txrxau/one-rom/hardware/pcb/verified/fire-24-f/README.md

# Fire 24 Rev F

A second USB-C variant, retaining the RP2354A MCU.

Changes from fire-24-e:
- Adds a neo-pixel LED, sharing GPIO 29 with the status LED.
- SEL pins have been swapped around for consistency with the latest 28, 32 and 40 pin designs.  The two right-most SEL pins are now ADC (non-5V tolerant) pins, with the othe two being 5V tolerant.
- A fraction of a mm narrower and shorter.
