txrxau/one-rom/rust/fw-emulator/build.rs

// Copyright (C) 2026 Piers Finlayson <piers@piers.rocks>
//
// MIT License

use std::{
    env,
    panic::{AssertUnwindSafe, catch_unwind},
    path::PathBuf,
    process::Command,
};

// Not defaults — used in error messages to show the caller what to set.
const EXAMPLE_CONFIG: &str = "onerom-config/test-0.json";
const EXAMPLE_BOARD: &str = "fire-24-a";

fn main() {
    let manifest_dir = PathBuf::from(env::var("CARGO_MANIFEST_DIR").unwrap());

    // Structure: project/rust/onerom-fw-emulator  →  two parents  →  project/
    let project_root = manifest_dir
        .parent()
        .expect("missing rust/ parent")
        .parent()
        .expect("missing project root")
        .to_path_buf();

    let c_root = project_root.join("firmware");

    let config = env::var("CONFIG")
        .unwrap_or_else(|_| panic!("CONFIG must be set (e.g. CONFIG={EXAMPLE_CONFIG})"));
    let board = env::var("BOARD")
        .unwrap_or_else(|_| panic!("BOARD must be set (e.g. BOARD={EXAMPLE_BOARD})"));

    // BASE_DIR is the project root used to resolve relative CONFIG paths and
    // ROM image files.  Defaults to the computed project_root so the Makefile
    // shell-script build works without change; set it explicitly when invoking
    // cargo from a different directory (e.g. BASE_DIR=$(realpath ../..) from
    // fw-tester/).
    let base_dir = if let Ok(bd) = env::var("BASE_DIR") {
        std::fs::canonicalize(&bd)
            .unwrap_or_else(|e| panic!("Cannot resolve BASE_DIR '{}': {}", bd, e))
    } else {
        project_root.clone()
    };

    // Resolve CONFIG to a canonical absolute path relative to base_dir.
    // Absolute paths are used as-is.
    let config_abs = {
        let p = PathBuf::from(&config);
        if p.is_absolute() {
            std::fs::canonicalize(&p)
                .unwrap_or_else(|e| panic!("Cannot find CONFIG '{}': {}", config, e))
        } else {
            std::fs::canonicalize(base_dir.join(&p)).unwrap_or_else(|e| {
                panic!(
                    "Cannot find CONFIG '{}' relative to BASE_DIR '{}': {}",
                    config,
                    base_dir.display(),
                    e
                )
            })
        }
    };

    // Re-run build.rs if these env vars change.
    println!("cargo:rerun-if-env-changed=CONFIG");
    println!("cargo:rerun-if-env-changed=BOARD");
    println!("cargo:rerun-if-env-changed=BASE_DIR");

    // ── C build ──────────────────────────────────────────────────────────────

    // Cargo sets CARGO_CFG_TARGET_ARCH to the *target* being built.  When that
    // is wasm we cross-compile the C library with Emscripten (for One ROM Lens)
    // into a separate build-wasm/, instead of the native host build-test/.  The
    // native path is unchanged.
    let is_wasm = env::var("CARGO_CFG_TARGET_ARCH").as_deref() == Ok("wasm32");
    let (make_target, clean_target, build_subdir) = if is_wasm {
        (
            "libonerom-test-wasm",
            "clean-libonerom-test-wasm",
            "build-wasm",
        )
    } else {
        ("libonerom-test", "clean-libonerom-test", "build-test")
    };

    println!(
        "cargo:rerun-if-changed={}",
        project_root.join("Makefile").display()
    );
    println!("cargo:rerun-if-changed={}", c_root.display());
    println!("cargo:rerun-if-changed={}", config_abs.display());
    println!(
        "cargo:rerun-if-changed={}",
        manifest_dir.join("src/wrapper.h").display()
    );

    // Clean the C library if CONFIG or BOARD has changed since the last build.
    // The Makefile has no visibility into these variables, so we track them
    // ourselves via a stamp file in the build output directory.
    let stamp_path = c_root.join(build_subdir).join(".build-config");
    let stamp = format!("CONFIG={}\nBOARD={board}\n", config_abs.display());
    let needs_clean = std::fs::read_to_string(&stamp_path)
        .map(|s| s != stamp)
        .unwrap_or(true);

    if needs_clean {
        let _ = Command::new("make")
            .arg("-C")
            .arg(&project_root)
            .arg(clean_target)
            .env("CONFIG", &config_abs)
            .env("BOARD", &board)
            .status()
            .expect("could not run make clean target");
    }

    let status = Command::new("make")
        .arg("-C")
        .arg(&project_root)
        .arg(make_target)
        .env("CONFIG", &config_abs)
        .env("BOARD", &board)
        .status()
        .expect("could not run make — is it on PATH?");
    assert!(
        status.success(),
        "make {make_target} failed (CONFIG={} BOARD={board})",
        config_abs.display()
    );

    std::fs::write(&stamp_path, &stamp).expect("could not write build stamp");

    // ── Linking ──────────────────────────────────────────────────────────────

    println!(
        "cargo:rustc-link-search=native={}",
        c_root.join(build_subdir).display()
    );
    println!("cargo:rustc-link-lib=static=onerom-test");
    // Emscripten provides libm as part of its libc; only the native build needs
    // an explicit -lm.
    if !is_wasm {
        println!("cargo:rustc-link-lib=m");
    }

    // ── bindgen ──────────────────────────────────────────────────────────────

    // Parse the firmware headers for the host explicitly, rather than leaving
    // libclang to use its own default target.  Two cases need this:
    //
    //   - Cross-compiling to wasm: cargo sets TARGET=wasm32-unknown-emscripten,
    //     so libclang would parse for the wasm target and fail to find the libc
    //     headers (string.h etc.), which live in the Emscripten sysroot.
    //   - A native build where LIBCLANG_PATH names a cross-toolchain's libclang
    //     (an ESP or AVR toolchain on PATH, say).  Its default target has no
    //     host sysroot, so the same headers go missing, and the pointer width
    //     it reports does not match the Rust target.
    //
    // We only need the C *declarations* — no by-value C structs cross the FFI
    // boundary whose layout differs between host and target — so parsing with
    // the host target and its system headers is safe.  bindgen emits
    // width-correct type aliases (c_long, usize, …) regardless of the parse
    // target.
    let builder = bindgen::Builder::default()
        .header(manifest_dir.join("src/wrapper.h").to_str().unwrap())
        .clang_arg(format!("--target={}", env::var("HOST").unwrap()));

    let builder = builder
        .clang_arg(format!("-I{}", c_root.join("include").display()))
        .clang_arg(format!("-I{}", c_root.join("generated").display()))
        .clang_arg(format!("-I{}", c_root.join("include/test").display()))
        .clang_arg(format!("-I{}", c_root.join("apio/include").display()))
        .clang_arg(format!("-I{}", c_root.join("epio/include").display()))
        .clang_arg(format!("-I{}", c_root.join("ora").display()))
        .clang_arg("-DTEST_BUILD=1".to_string())
        .clang_arg("-DDEBUG_LOGGING=1".to_string())
        .allowlist_function("firmware_main")
        .allowlist_function("epio_from_apio")
        .allowlist_function("epio_get_sram_ptr")
        .allowlist_function("epio_update_from_apio")
        .allowlist_function("epio_drive_gpios_ext")
        .allowlist_function("epio_read_pin_states")
        .allowlist_function("epio_step_cycles")
        .allowlist_function("epio_free")
        .allowlist_function("epio_read_driven_pins")
        .allowlist_function("epio_read_pull_up_pins")
        .allowlist_function("epio_read_pull_down_pins")
        .allowlist_function("epio_disassemble_sm")
        .allowlist_function("epio_get_gpio_input_inverted")
        .allowlist_function("set_host_sram_ptr")
        .allowlist_function("stub_set_sel_image")
        .allowlist_function("stub_set_rp_variant")
        .allowlist_function("ffi_limp_mode")
        .allowlist_function("ffi_pios_enabled")
        .allowlist_function("ffi_image_sel")
        .allowlist_function("ffi_epio_setup_sram")
        .allowlist_function("ffi_epio_setup_dma_chain")
        .allowlist_function("ffi_epio_arm_monitor")
        .allowlist_function("set_onerom_test_yield_hook")
        .allowlist_function("ffi_set_logging")
        .allowlist_function("ffi_serving_alg")
        .allowlist_type("ffi_serving_alg_t")
        // The algorithm enums the reported ids belong to: a test that maps an
        // id to an expected cycle cost must name the enumerators rather than
        // hardcode their values.
        .allowlist_type("onerom_alg_cs_t")
        .allowlist_type("onerom_alg_addr_t")
        .allowlist_type("onerom_alg_data_t")
        .allowlist_function("ora_fn_lookup")
        .allowlist_type("ora_result_t")
        .allowlist_type("ora_.*_fn_t")
        // ora_gpio_use_t / ora_gpio_state_t are referenced only from comments
        // and uint8_t struct fields, so nothing drags them in transitively.
        // The plugin API tester compares ora_gpio_query's reported use against
        // the apio emulation's own record, and must name the enumerators
        // rather than hardcode their values.
        .allowlist_type("ora_gpio_.*_t")
        // The apio emulation's record of how the firmware configured the PIO
        // blocks and the GPIOs.  This is what serving actually did, as opposed
        // to what the slot configuration says it should have done, and is the
        // plugin API tester's independent oracle for the GPIO classification.
        .allowlist_var("_apio_emulated_pio")
        .allowlist_var("_apio_emulated_gpios")
        .allowlist_function("ffi_runtime_info_ptr")
        .allowlist_function("ffi_runtime_info_size")
        .parse_callbacks(Box::new(bindgen::CargoCallbacks::new()));

    // bindgen *panics* - it does not return an error - when it cannot load
    // libclang, and the message it prints names only the LIBCLANG_PATH
    // environment variable, not the package that provides the library.  Catch
    // the panic so we can say which one to install.  By the time catch_unwind
    // returns, the default hook has already printed bindgen's own message, so
    // this adds to it rather than replacing it.  AssertUnwindSafe is sound
    // because the build is abandoned in the panicking case either way.
    let generated = catch_unwind(AssertUnwindSafe(|| builder.generate()));

    let bindings = match generated {
        Ok(Ok(bindings)) => bindings,
        Ok(Err(e)) => panic!("bindgen failed to generate bindings: {e}"),
        Err(_) => {
            eprintln!();
            eprintln!("onerom-fw-emulator generates its FFI bindings from the firmware C");
            eprintln!("headers at build time, so libclang must be installed:");
            eprintln!();
            eprintln!("    Debian/Ubuntu   sudo apt-get install libclang-dev");
            eprintln!("    Fedora          sudo dnf install clang-devel");
            eprintln!("    Arch            sudo pacman -S clang");
            eprintln!("    macOS           xcode-select --install (or: brew install llvm)");
            eprintln!();
            eprintln!("If libclang is installed somewhere unusual, set LIBCLANG_PATH to the");
            eprintln!("directory holding libclang.so (libclang.dylib on macOS).");
            std::process::exit(1);
        }
    };

    let out_dir = PathBuf::from(env::var("OUT_DIR").unwrap());
    bindings
        .write_to_file(out_dir.join("bindings.rs"))
        .expect("could not write bindings.rs");
}
